Tristand1220/EweGo/Hardware/Case/uCM4-update.step

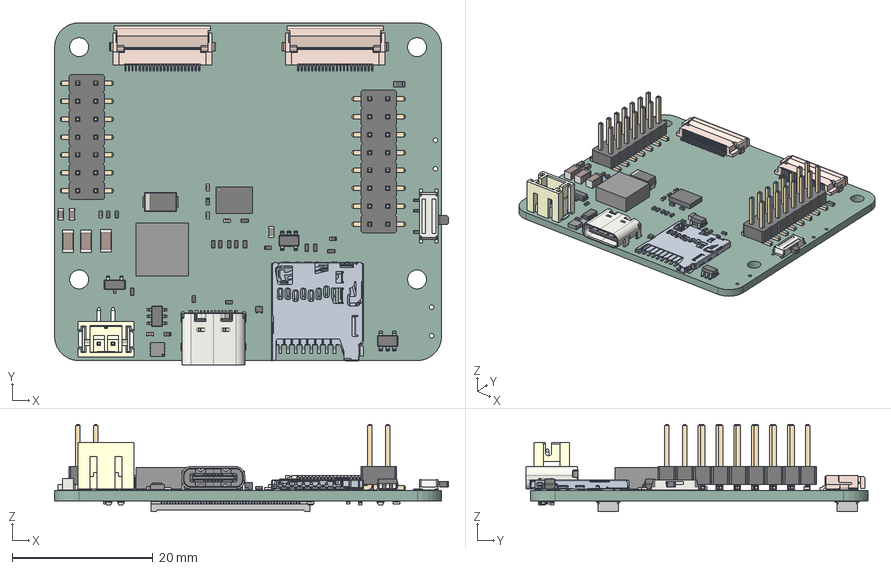
[picture p17: CAD file, 2026-02-17]
Hardware/Case/uCM4-update.step
56.0 x 48.6 x 12.4 mm
SOT-23-5 x 2
R_0402_1005Metric x 22
LGA-28_5.2x3.8mm_P0.5mm
C_0603_1608Metric x 3
C_1206_3216Metric x 3
USB_C_Receptacle_GCT_USB4105-xx-A_16P_TopMnt_Horizontal
C_0402_1005Metric x 5
Texas_DRT-3
TSOT-23-6
FH12-22S-0.5SH_Èª x 2
Pins
PinHeader_2x07_P2.54mm_Vertical_SMD
D_SMA
SW_SPDT_PCM12
R_0603_1608Metric
ThermalPin
PinsArrayLR
B2B-PH-SM4-TB_B2B-PH-SM4-TB
SOT-23
PinHeader_2x08_P2.54mm_Vertical_SMD
LED_0402_1005Metric x 5
DF40C-100DS x 2
uCM4_PCB
