Tristand1220/EweGo/Hardware/Case/AssemblyParts/raspberry-pi-5mp-camera-module-1.snapshot.1/Camera Module Assem.STEP

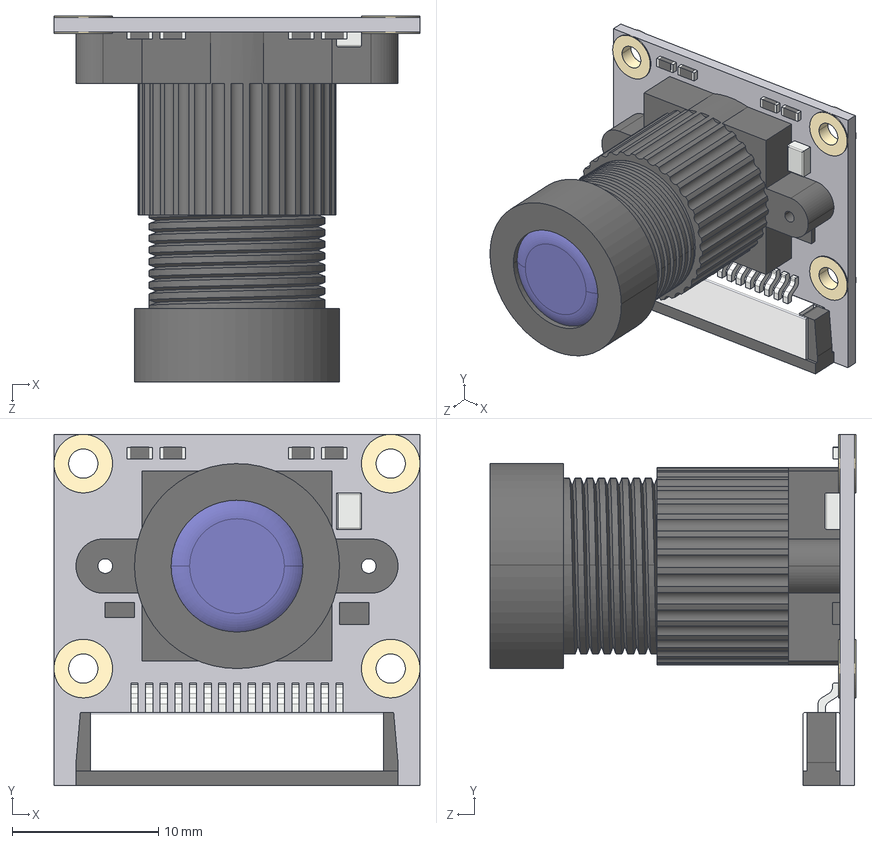
[picture p18: CAD file, 2026-02-17]
Hardware/Case/AssemblyParts/raspberry-pi-5mp-camera-module-1.snapshot.1/Camera Module Assem.STEP
25.0 x 24.0 x 25.0 mm
PCB 1
Camera Block
Camera end
Lenz
15 Pin Ribbon Block
Ribbon Clamp
0603 Resistor x 4
