Tristand1220/EweGo/Hardware/Case/LeftCamera.SLDPRT

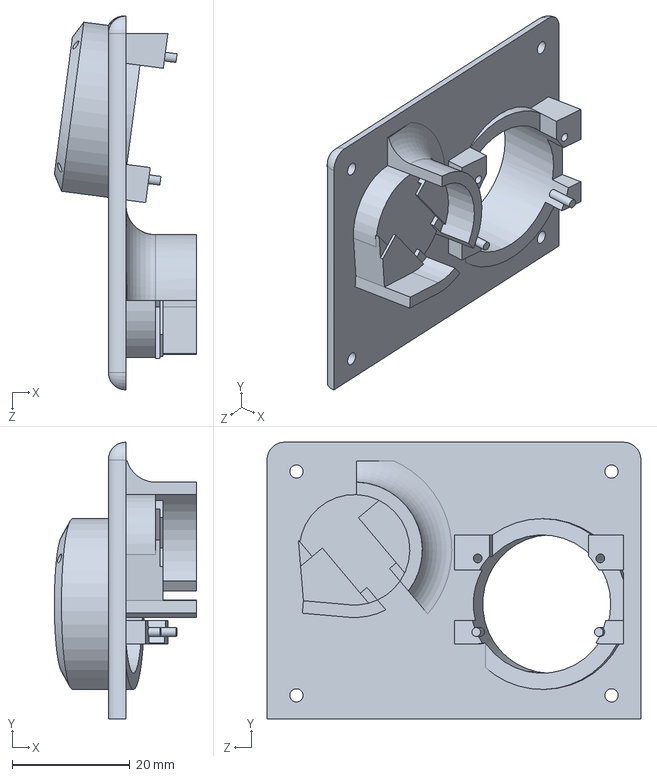
[picture p19: CAD file, 2026-02-17]
Hardware/Case/LeftCamera.SLDPRT
24.2 x 47.0 x 63.5 mm
