Tristand1220/EweGo/Hardware/Case/AssemblyParts/raspberry-pi-5mp-camera-module-1.snapshot.1/Camera end.SLDPRT

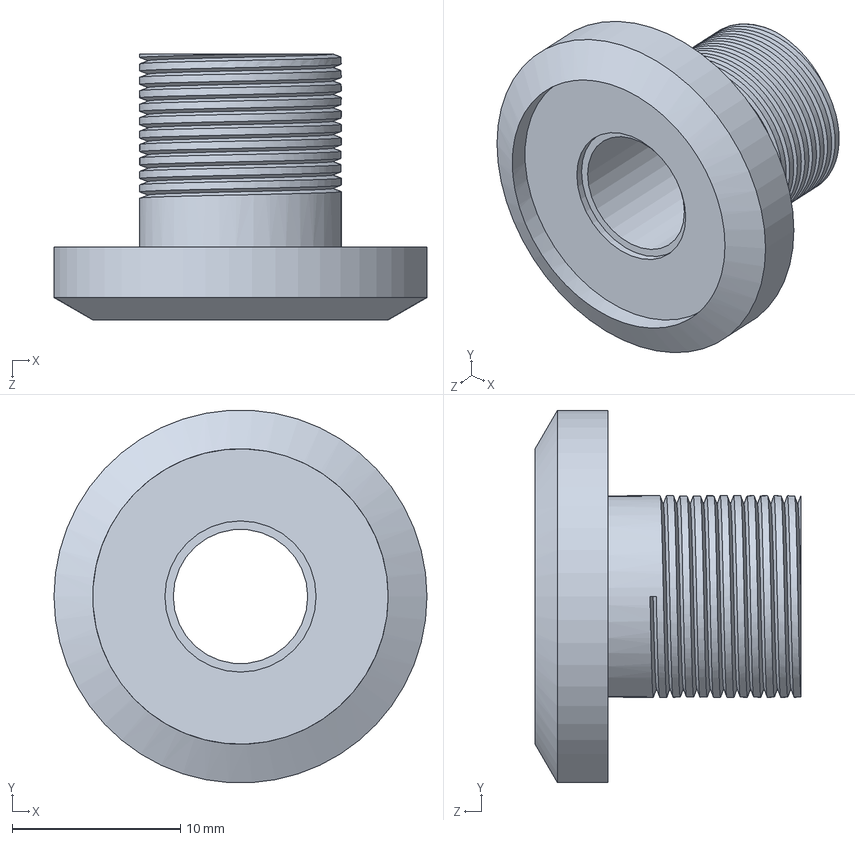
[picture p20: CAD file, 2026-02-17]
Hardware/Case/AssemblyParts/raspberry-pi-5mp-camera-module-1.snapshot.1/Camera end.SLDPRT
22.2 x 22.2 x 15.8 mm
