Tristand1220/EweGo/Hardware/Case/Frame.SLDPRT

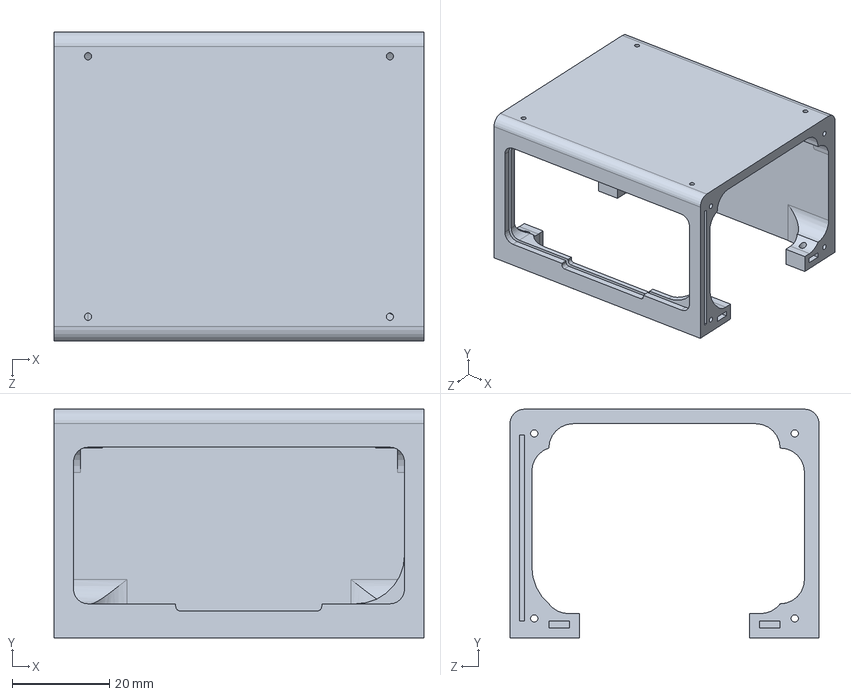
[picture p21: CAD file, 2026-02-17]
Hardware/Case/Frame.SLDPRT
76.0 x 47.0 x 63.5 mm
